argusro/pi0companion/code_esp/logo.h

// 'Bah_TL', 128x32px
const unsigned char bah_TL [] PROGMEM = {
  0x00, 0x00, 0x00, 0x00, 0x00, 0x00, 0x00, 0x00, 0x00, 0x00, 0x00, 0x00, 0x00, 0x00, 0x00, 0x00, 
  0x00, 0x00, 0x00, 0x00, 0x00, 0x00, 0x00, 0x00, 0x00, 0x00, 0x00, 0x00, 0x00, 0x00, 0x00, 0x00, 
  0x03, 0x80, 0x03, 0xf0, 0x1c, 0x10, 0x00, 0x00, 0x00, 0x00, 0x00, 0x00, 0x00, 0x00, 0x00, 0x00, 
  0x03, 0xe0, 0x0f, 0xfc, 0x1c, 0x30, 0x00, 0x00, 0x00, 0x00, 0x00, 0x00, 0x00, 0x00, 0x00, 0x00, 
  0x01, 0xe0, 0x1c, 0x1e, 0x0c, 0x10, 0x00, 0x00, 0x00, 0x00, 0x00, 0x00, 0x00, 0x00, 0x00, 0x00, 
  0x01, 0xb0, 0x18, 0x07, 0x0c, 0x10, 0x00, 0x00, 0x00, 0x00, 0x00, 0x00, 0x00, 0x00, 0x00, 0x00, 
  0x01, 0xb0, 0x30, 0x03, 0x0c, 0x10, 0x00, 0x00, 0x00, 0x00, 0x00, 0x00, 0x00, 0x00, 0x00, 0x00, 
  0x01, 0x90, 0x30, 0x03, 0x0c, 0x10, 0x00, 0x00, 0x00, 0x00, 0x00, 0x00, 0x00, 0x00, 0x00, 0x00, 
  0x01, 0x98, 0x31, 0xf1, 0x0c, 0x10, 0x03, 0xf0, 0x00, 0x00, 0x01, 0x00, 0x00, 0x00, 0x00, 0x00, 
  0x01, 0x98, 0x63, 0xf9, 0x8c, 0x10, 0x00, 0x44, 0x00, 0x00, 0x01, 0x00, 0x00, 0x00, 0x00, 0x00, 
  0x01, 0x98, 0x63, 0x39, 0x8c, 0x10, 0x00, 0x40, 0x00, 0x00, 0x01, 0x00, 0x00, 0x00, 0x00, 0x00, 
  0x01, 0xb0, 0x66, 0x19, 0x8c, 0x10, 0x00, 0x40, 0x00, 0x00, 0x01, 0x00, 0x00, 0x00, 0x00, 0x00, 
  0x01, 0xb0, 0x66, 0x11, 0x8c, 0x10, 0x00, 0x44, 0x58, 0xc1, 0xe1, 0x1f, 0x07, 0xc3, 0xe1, 0xf0, 
  0x01, 0xf0, 0x6c, 0x31, 0x8f, 0xf8, 0x00, 0x44, 0x43, 0x22, 0x09, 0x20, 0x98, 0x24, 0x12, 0x08, 
  0x03, 0xe0, 0x6c, 0x31, 0x8f, 0xf8, 0x00, 0x44, 0x40, 0x23, 0x09, 0x20, 0x98, 0x24, 0x03, 0x08, 
  0x01, 0xf0, 0x6c, 0x31, 0x8c, 0x10, 0x00, 0x44, 0x40, 0x22, 0xf9, 0x20, 0x98, 0x23, 0xc2, 0x78, 
  0x01, 0xb8, 0x6c, 0x31, 0x84, 0x10, 0x00, 0x44, 0x40, 0x20, 0x01, 0x20, 0x88, 0x20, 0x02, 0x00, 
  0x01, 0x9c, 0x6c, 0x31, 0x8c, 0x10, 0x00, 0x44, 0x44, 0x22, 0x01, 0x20, 0x98, 0x20, 0x12, 0x00, 
  0x01, 0x8c, 0x6c, 0x39, 0x8c, 0x10, 0x00, 0x44, 0x40, 0x20, 0x01, 0x21, 0x8c, 0x04, 0x12, 0x00, 
  0x01, 0x86, 0x6c, 0x3f, 0x8c, 0x10, 0x00, 0x44, 0xc4, 0x21, 0xf1, 0x1e, 0x9b, 0xc3, 0xe1, 0xf0, 
  0x01, 0x86, 0x6e, 0x7f, 0x0c, 0x10, 0x00, 0x00, 0x00, 0x00, 0x00, 0x00, 0x08, 0x00, 0x00, 0x00, 
  0x01, 0x86, 0x67, 0x66, 0x0c, 0x18, 0x00, 0x00, 0x00, 0x00, 0x00, 0x00, 0x18, 0x00, 0x00, 0x00, 
  0x01, 0x86, 0x63, 0xc0, 0x0c, 0x18, 0x00, 0x00, 0x00, 0x00, 0x00, 0x00, 0x08, 0x00, 0x00, 0x00, 
  0x01, 0x86, 0x70, 0x00, 0x04, 0x18, 0x00, 0x00, 0x00, 0x00, 0x00, 0x00, 0x08, 0x00, 0x00, 0x00, 
  0x01, 0x86, 0x30, 0x06, 0x04, 0x18, 0x00, 0x00, 0x00, 0x00, 0x00, 0x00, 0x00, 0x00, 0x00, 0x00, 
  0x01, 0x86, 0x38, 0x06, 0x04, 0x18, 0x00, 0x00, 0x00, 0x00, 0x00, 0x00, 0x00, 0x00, 0x00, 0x00, 
  0x01, 0x86, 0x1e, 0x06, 0x04, 0x18, 0x00, 0x00, 0x00, 0x00, 0x00, 0x00, 0x00, 0x00, 0x00, 0x00, 
  0x01, 0x8c, 0x0f, 0x9c, 0x04, 0x18, 0x00, 0x00, 0x00, 0x00, 0x00, 0x00, 0x00, 0x00, 0x00, 0x00, 
  0x01, 0xfc, 0x07, 0xfc, 0x04, 0x18, 0x00, 0x00, 0x00, 0x00, 0x00, 0x00, 0x00, 0x00, 0x00, 0x00, 
  0x01, 0xf0, 0x01, 0xf8, 0x04, 0x18, 0x00, 0x00, 0x00, 0x00, 0x00, 0x00, 0x00, 0x00, 0x00, 0x00, 
  0x00, 0x00, 0x00, 0x00, 0x00, 0x00, 0x00, 0x00, 0x00, 0x00, 0x00, 0x00, 0x00, 0x00, 0x00, 0x00, 
  0x00, 0x00, 0x00, 0x00, 0x00, 0x00, 0x00, 0x00, 0x00, 0x00, 0x00, 0x00, 0x00, 0x00, 0x00, 0x00
};
